Totof34/Bobineuse_V3/images/PCB_Mot_pàp_cablé.JPG

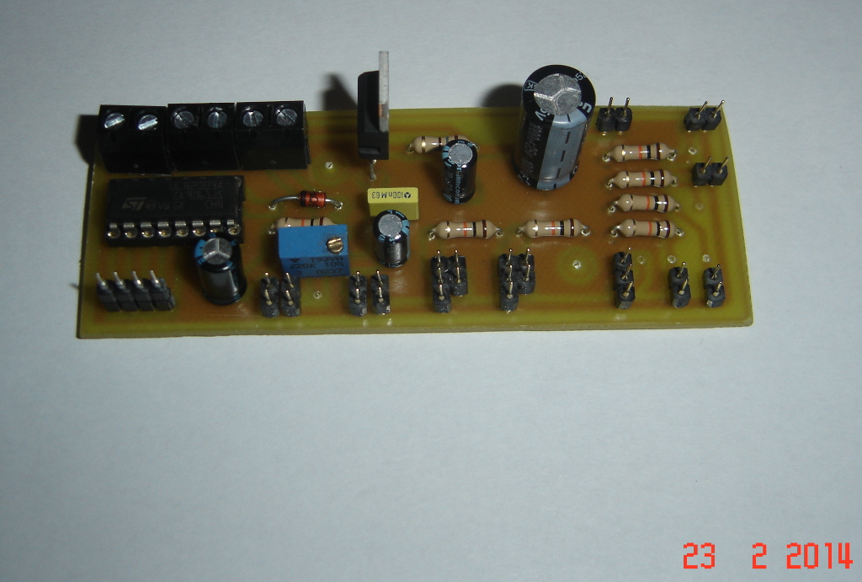
images/PCB_Mot_pàp_cablé.JPG
