Totof34/Bobineuse_V3/images/Proto_compteur_roue1.JPG

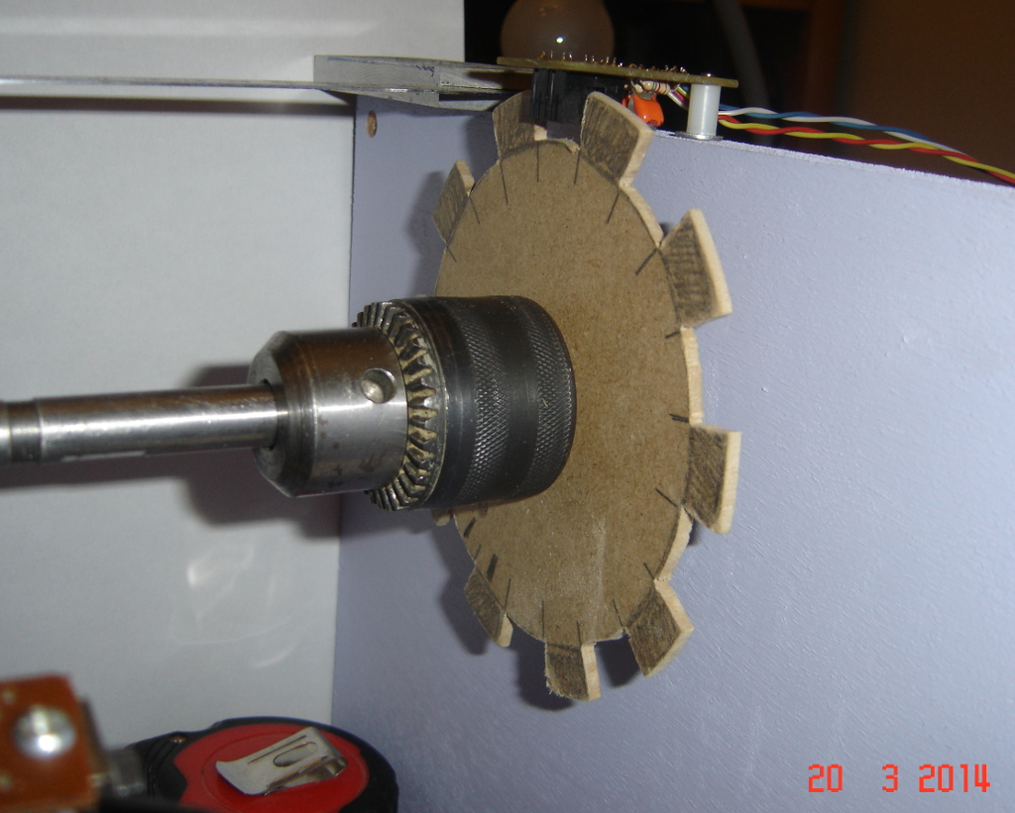
images/Proto_compteur_roue1.JPG
