Totof34/Bobineuse_V3/images/Proto_facade1.JPG

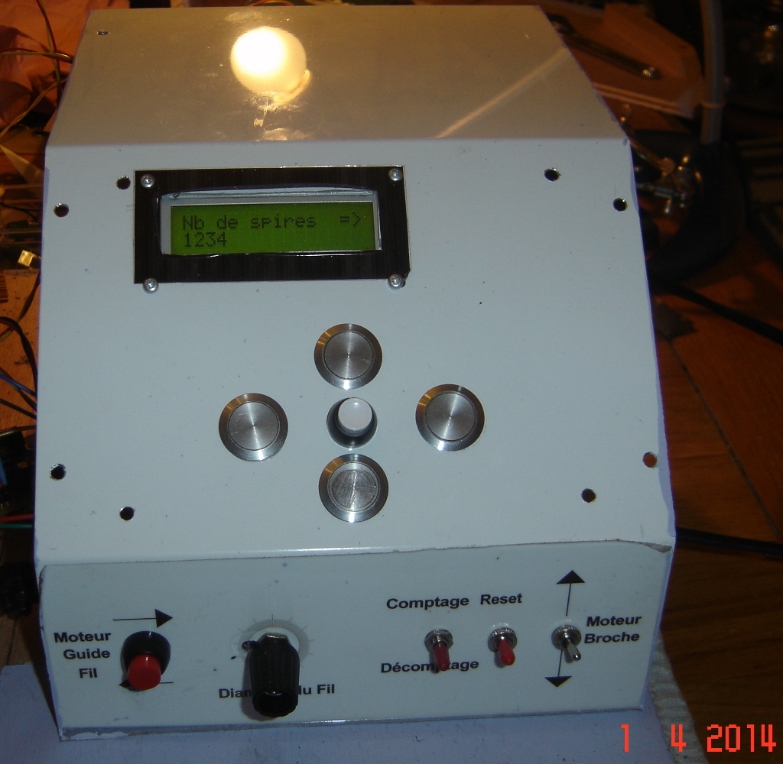
images/Proto_facade1.JPG
