Totof34/Bobineuse_V3/schematics/1Hr4k.png

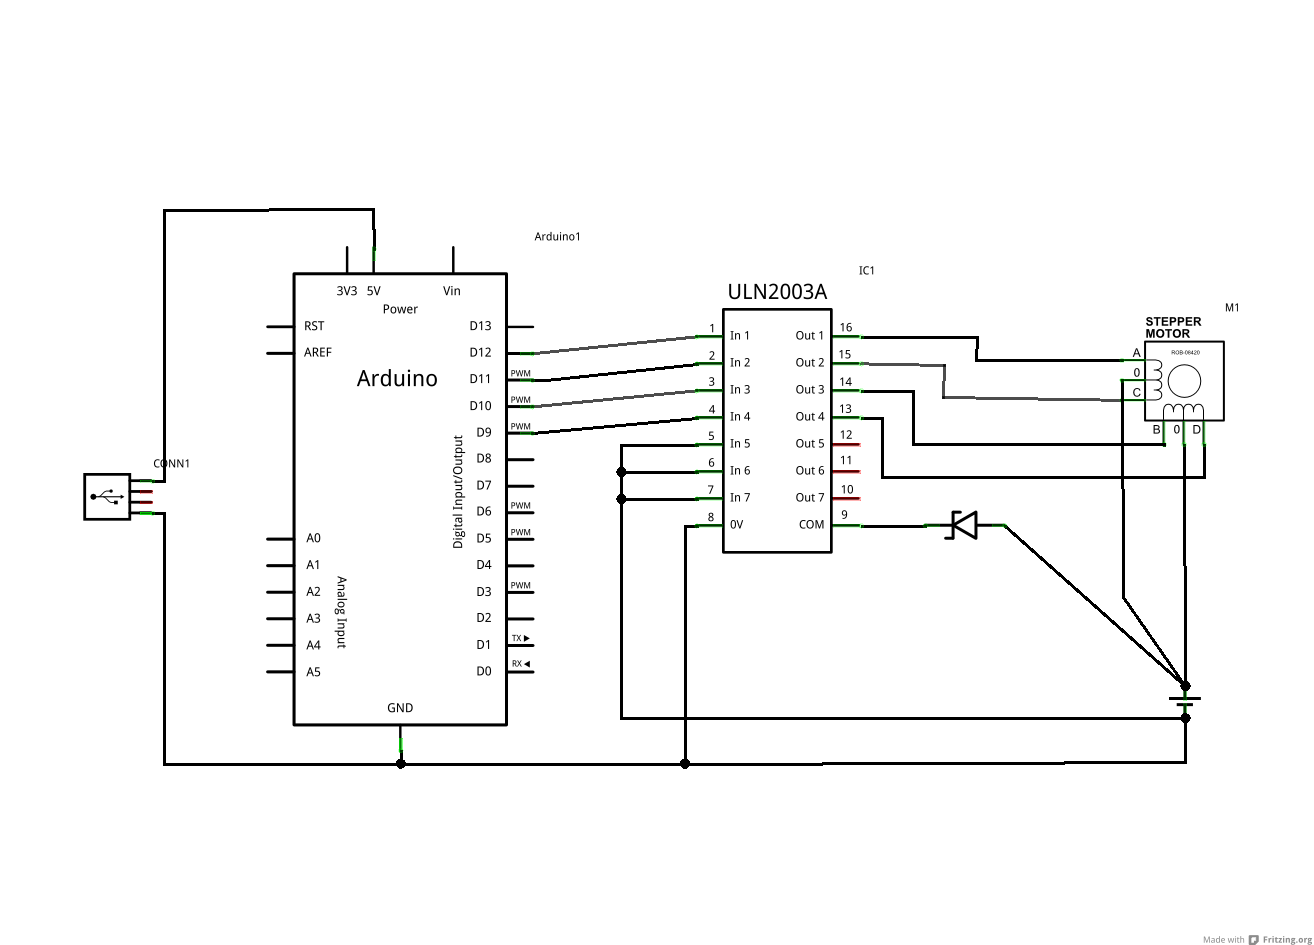
schematics/1Hr4k.png
