Totof34/Bobineuse_V3/build/Facade bobineuse V3 full.JPG

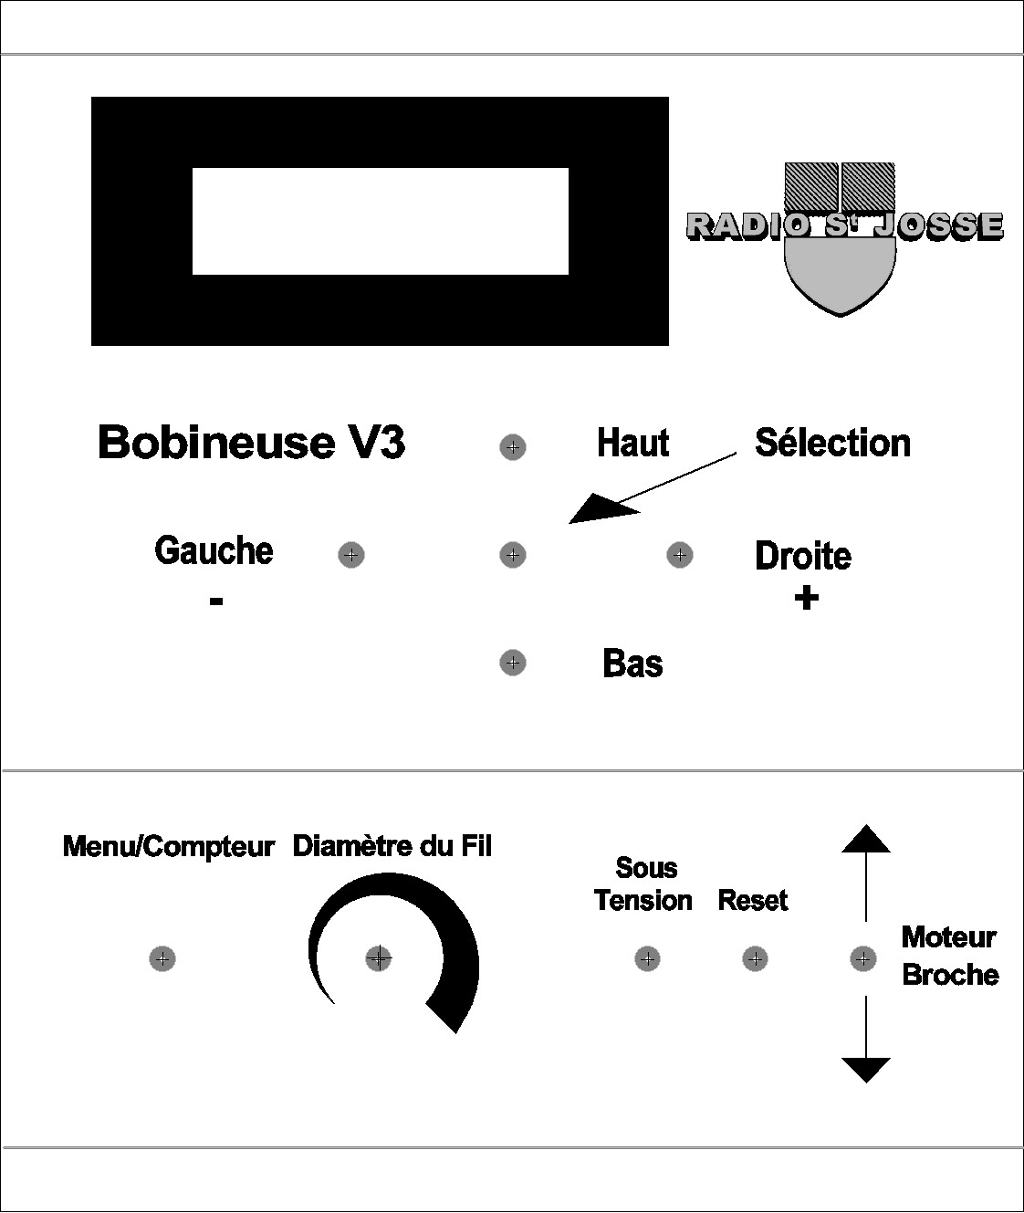
build/Facade bobineuse V3 full.JPG
