Totof34/Bobineuse_V3/images/Reconstruction_bobineuse_V3_6.JPG

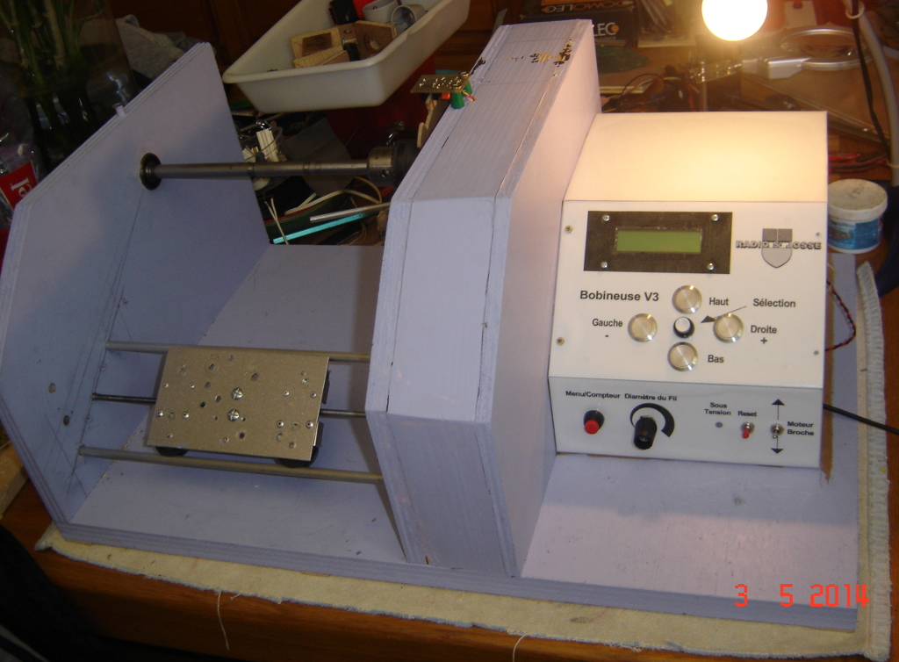
images/Reconstruction_bobineuse_V3_6.JPG
