Totof34/Bobineuse_V3/images/Reconstruction_bobineuse_V3_12.JPG

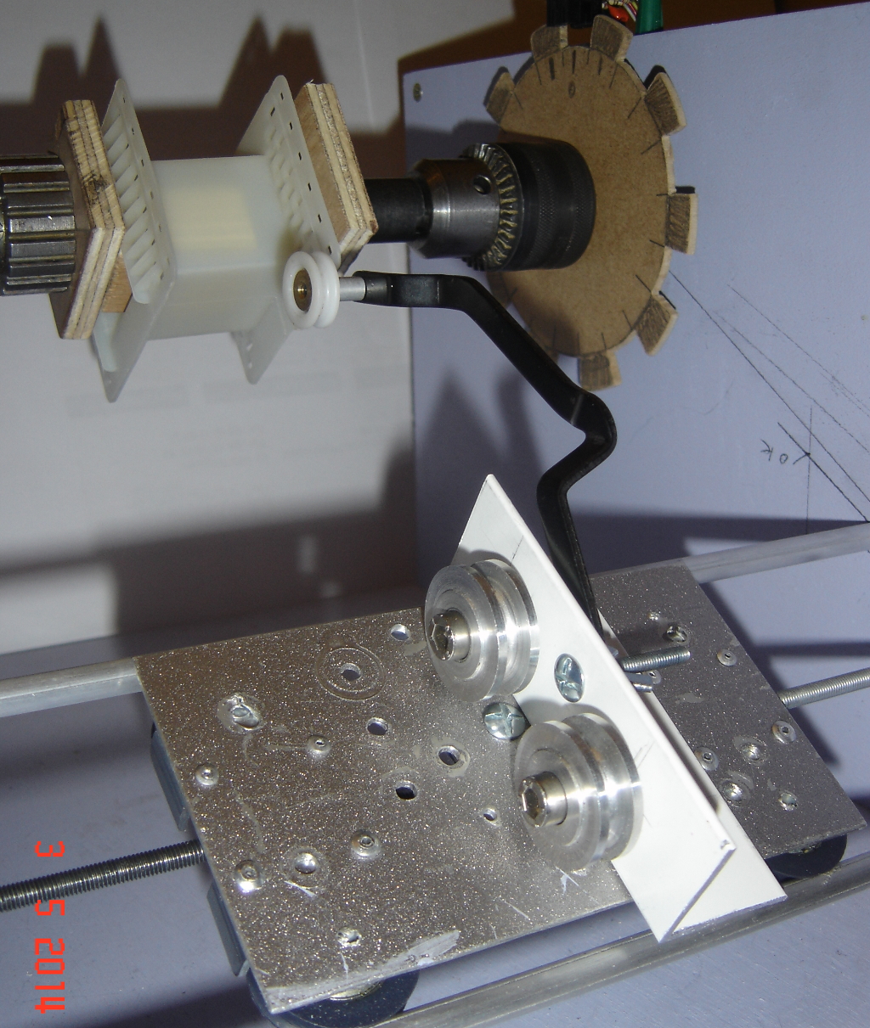
images/Reconstruction_bobineuse_V3_12.JPG
